YfNk1d5up/piJag/Pictures/modPCB.png

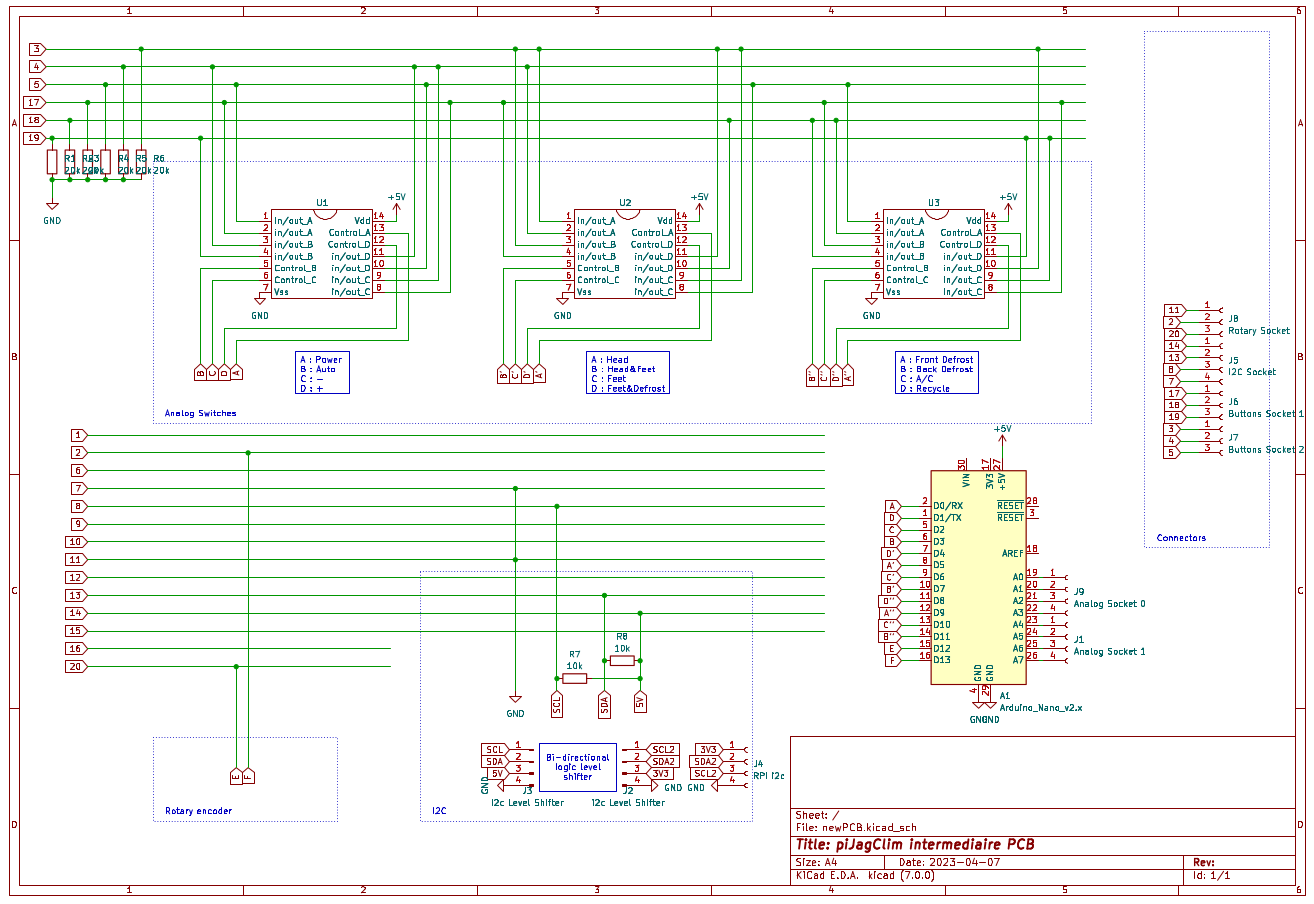
Pictures/modPCB.png
