YfNk1d5up/piJag/Pictures/PCB3D.png

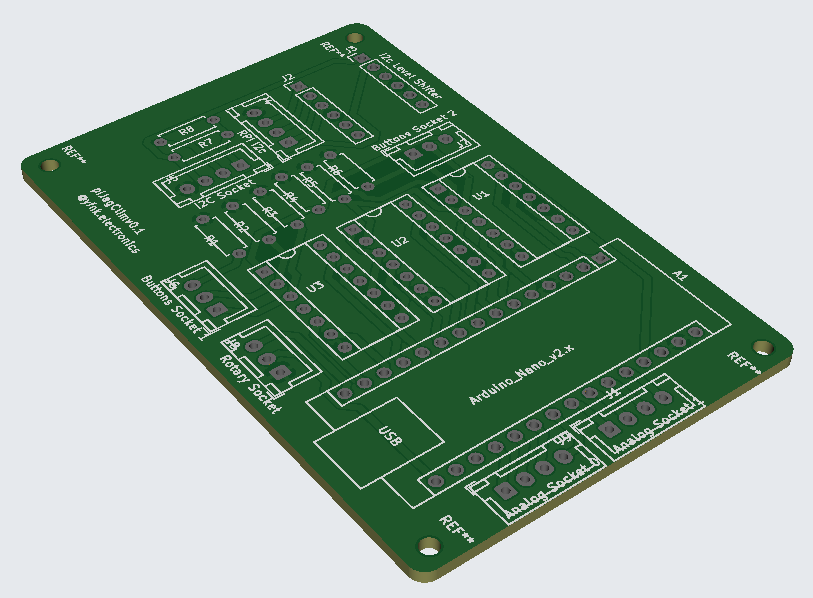
Pictures/PCB3D.png
