YfNk1d5up/piJag/Pictures/PCBBottom.png

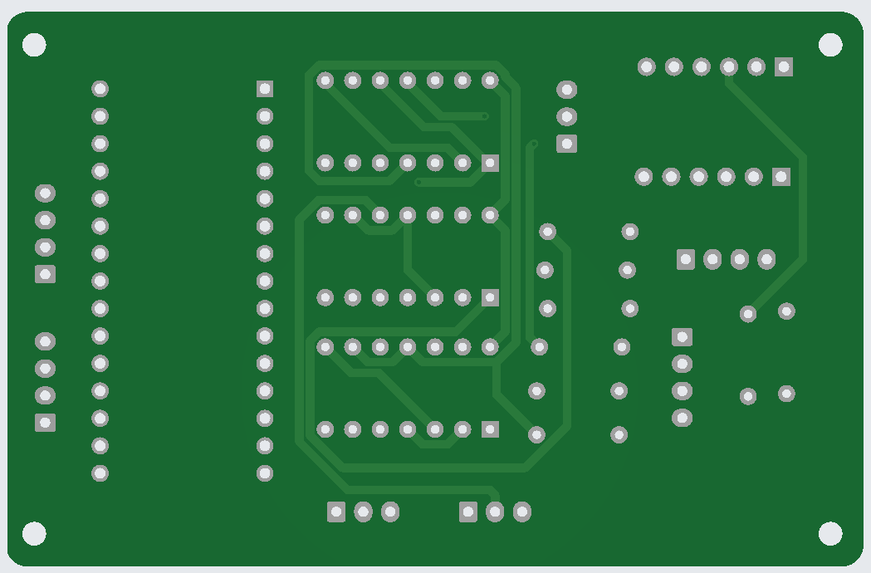
Pictures/PCBBottom.png
