YfNk1d5up/piJag/Pictures/PCBmounted3d.jpeg

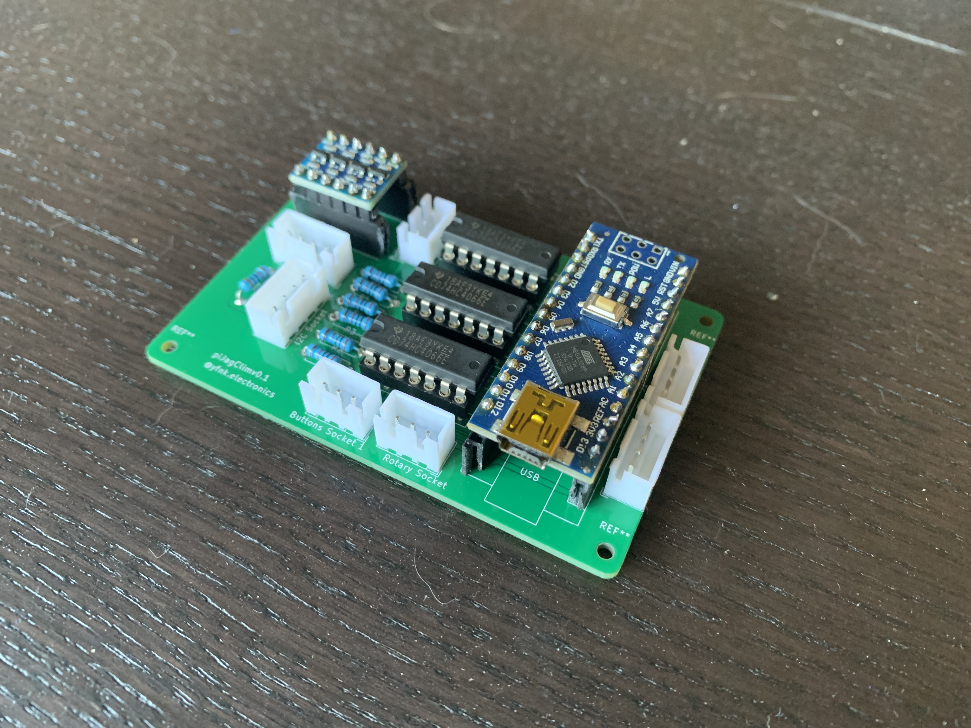
Pictures/PCBmounted3d.jpeg
