YfNk1d5up/piJag/Pictures/PCBTop.png

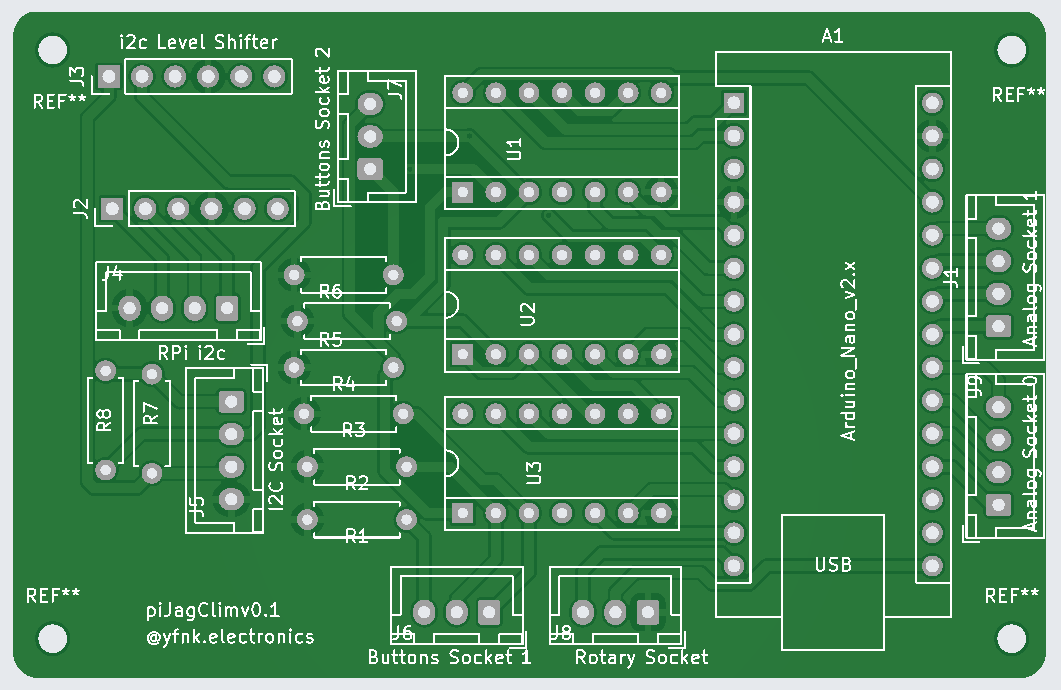
Pictures/PCBTop.png
