YfNk1d5up/piJag/Pictures/qtPiJagClimApp_v0.1.png

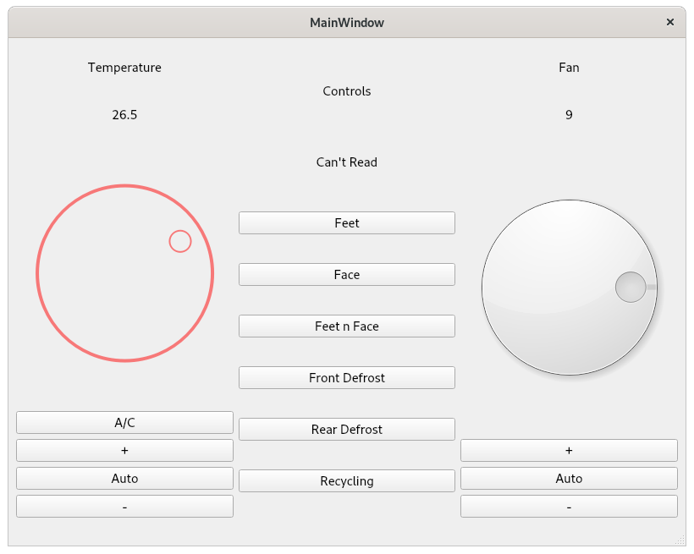
Pictures/qtPiJagClimApp_v0.1.png
