YfNk1d5up/piJag/Pictures/qtPiJagClimApp_v0.11.png

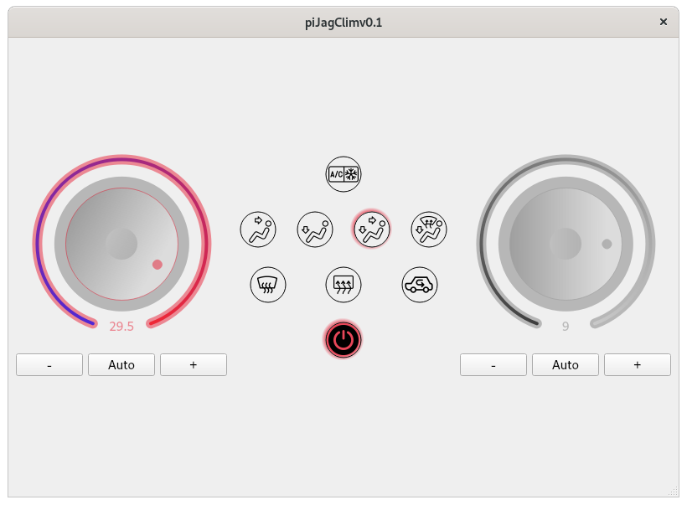
Pictures/qtPiJagClimApp_v0.11.png
