YfNk1d5up/piJag/Pictures/sda_scl_oscillo.png

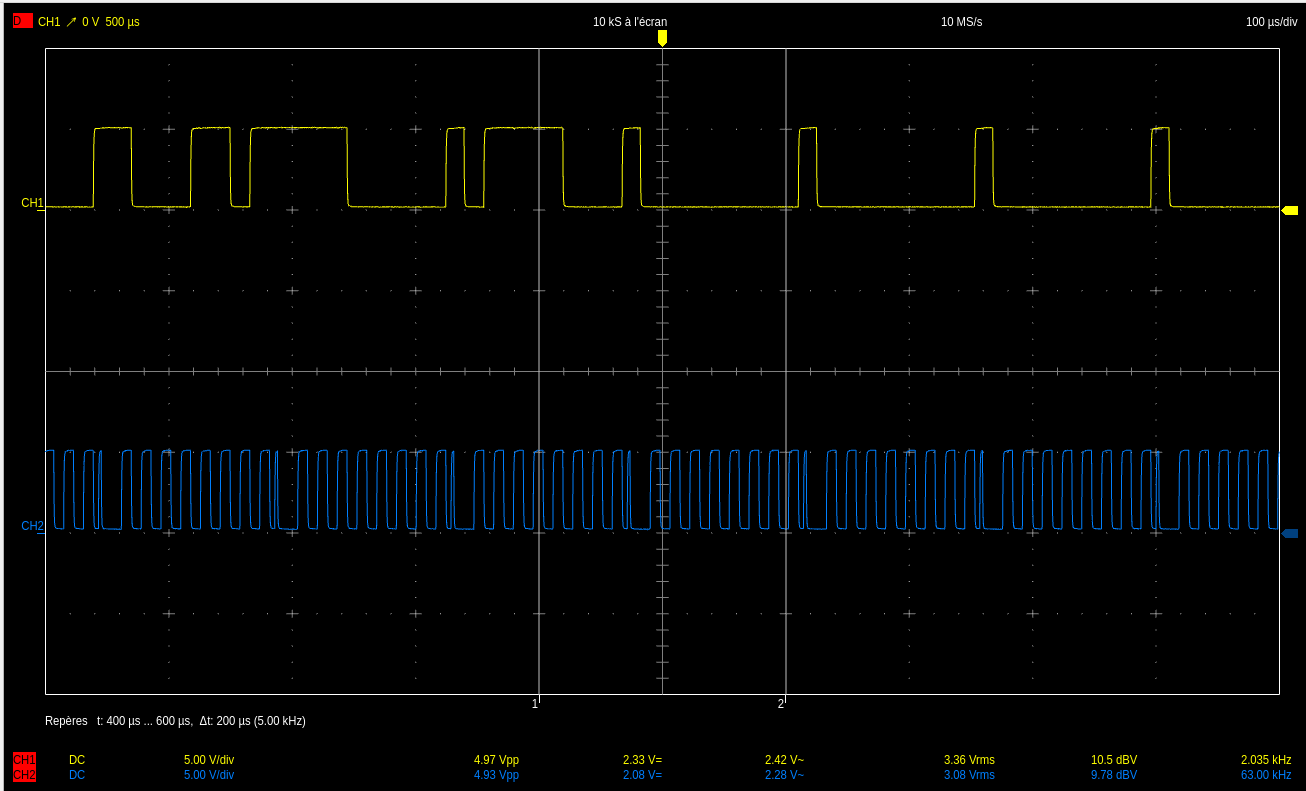
Pictures/sda_scl_oscillo.png
