YfNk1d5up/piJag/Software/piJagClimApp/v0.2/pictures/AC.png

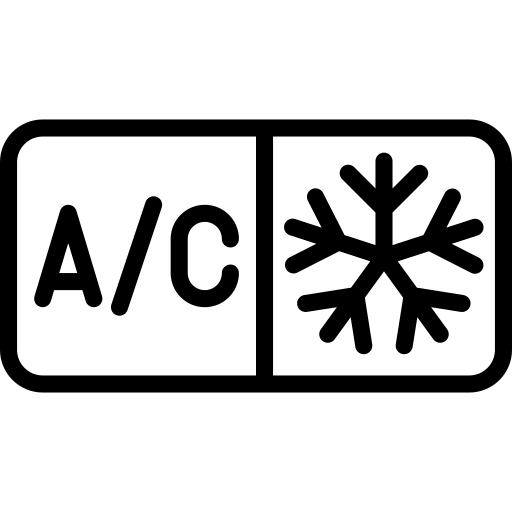
Software/piJagClimApp/v0.2/pictures/AC.png
