YfNk1d5up/piJag/Software/piJagClimApp/v0.2/pictures/face.png

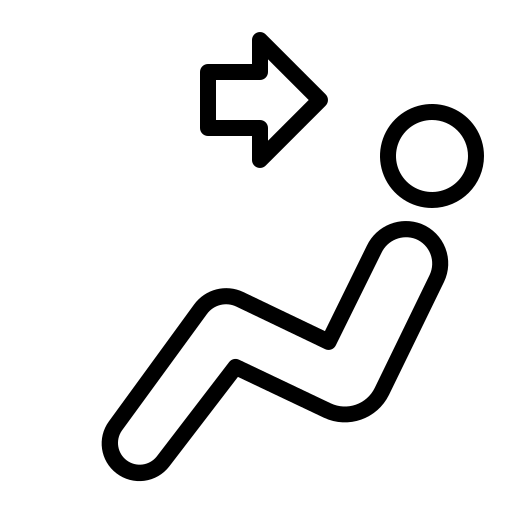
Software/piJagClimApp/v0.2/pictures/face.png
