YfNk1d5up/piJag/Software/piJagClimApp/v0.2/pictures/front_feet.png

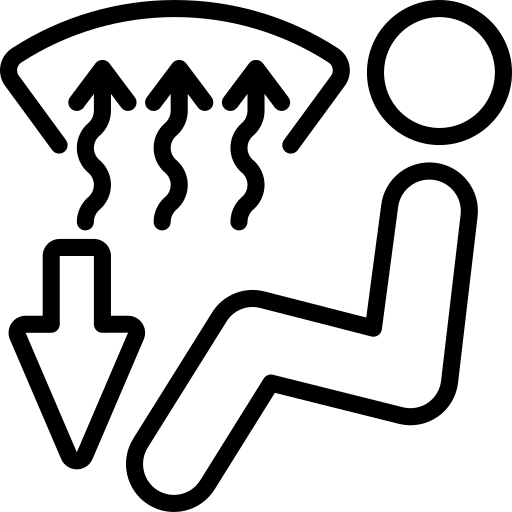
Software/piJagClimApp/v0.2/pictures/front_feet.png
