YfNk1d5up/piJag/Software/piJagClimApp/v0.2/pictures/power.png

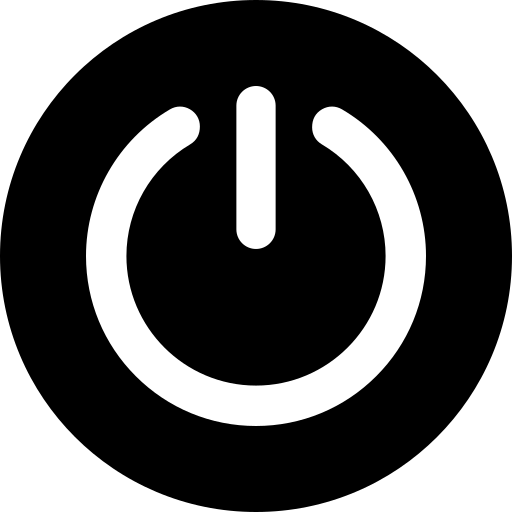
Software/piJagClimApp/v0.2/pictures/power.png
