YfNk1d5up/piJag/Software/piJagClimApp/v0.2/pictures/rear.png

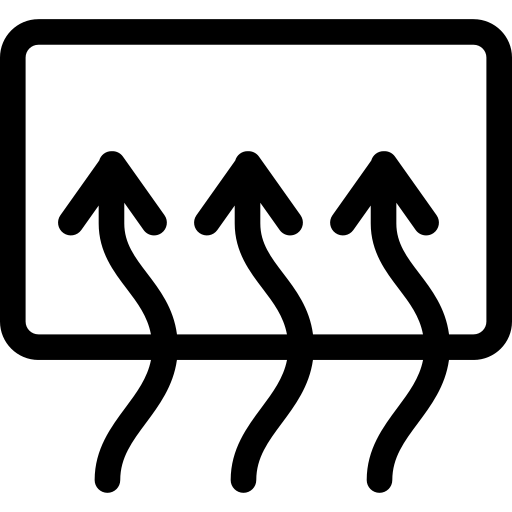
Software/piJagClimApp/v0.2/pictures/rear.png
