YfNk1d5up/piJag/Software/piJagClimApp/v0.2/pictures/recycle.png

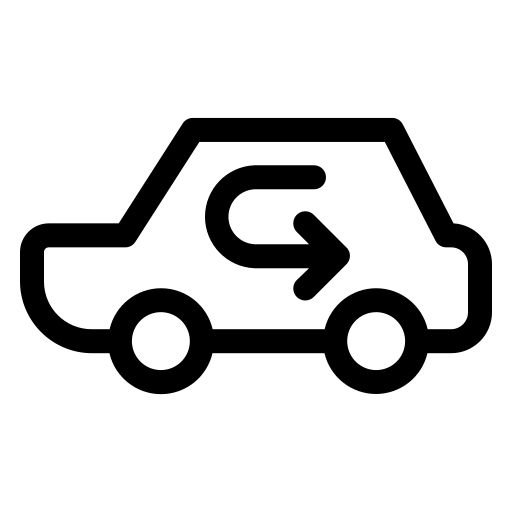
Software/piJagClimApp/v0.2/pictures/recycle.png
