YfNk1d5up/piJag/Hardware/piJagClim/nano_sniffer/piJagClimSniffer/I2CSNIFF.h

#ifndef	_i2csniff_h_
#define	_i2csniff_h_

#define	START	's'
#define	ACK	'a'
#define	NACK	'n'
#define	STOP	"p"


void init_i2c( void );
void putnibble( u8 j );
void i2c_sniff( void );
void i2c_sniff_new( void );
void i2c_sniff_single( void );
void i2c_sniff_sm( void );
#endif
